godor2008/MFD_3/MFD/Image/title.jpg

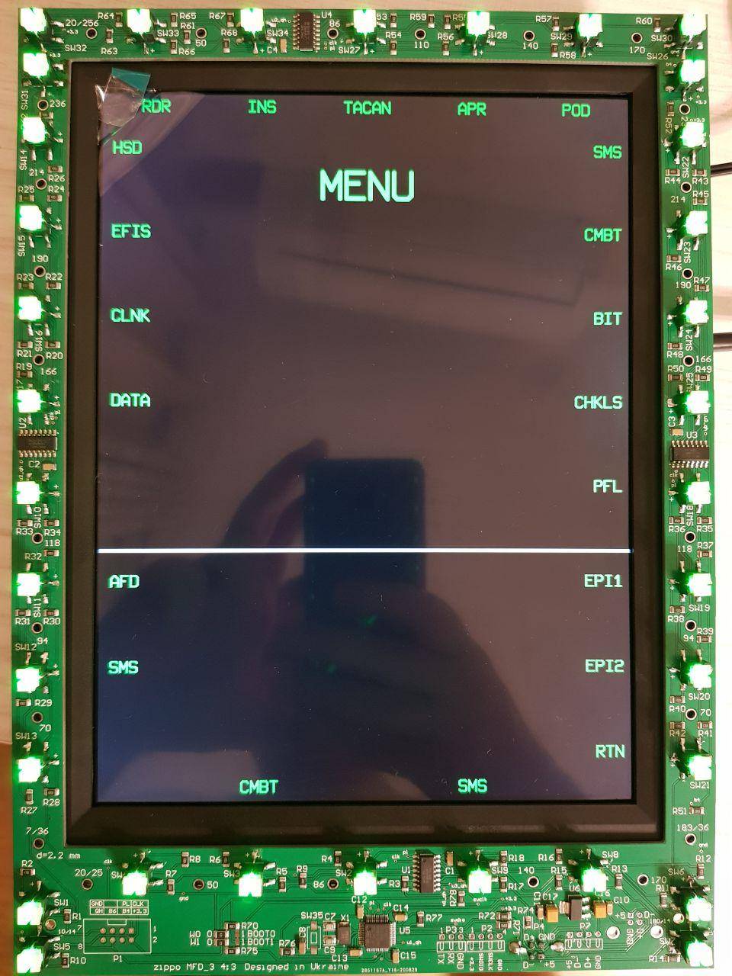
MFD/Image/title.jpg
